marsairforce/radioshack_homemade_linear_power_supply/updated/IMG_0323.jpg

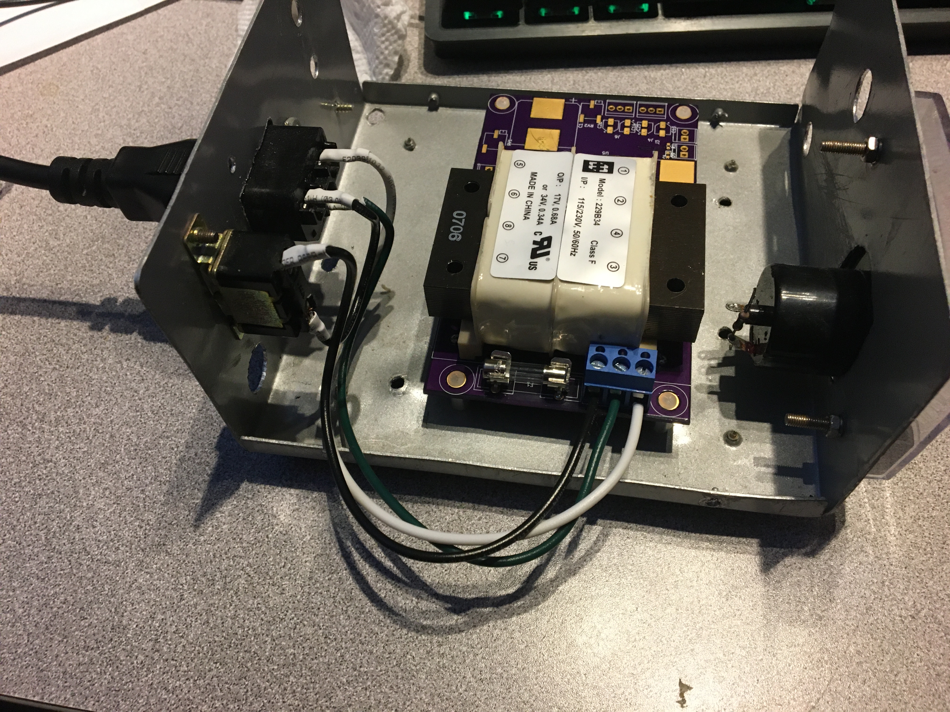
updated/IMG_0323.jpg
