marsairforce/radioshack_homemade_linear_power_supply/updated/opamp_power_supply/IMG_0309.jpg

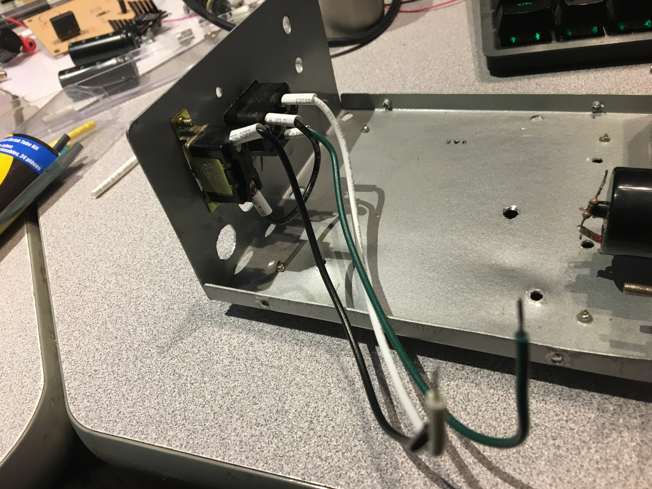
updated/opamp_power_supply/IMG_0309.jpg
